Grigoriym/esp32-desk-display/enclosure/renders/enclosure-back.png

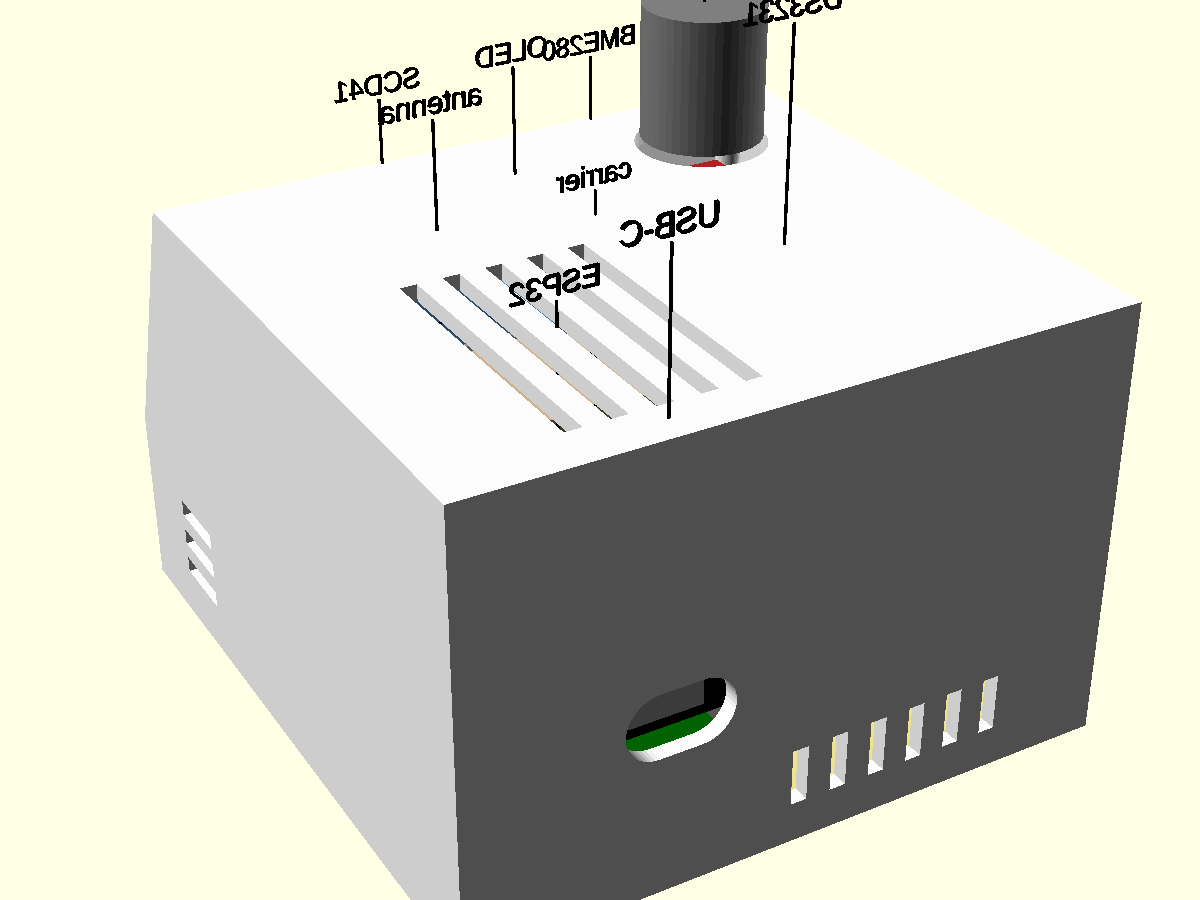
enclosure/renders/enclosure-back.png
