Grigoriym/esp32-desk-display/enclosure/renders/enclosure-section.png

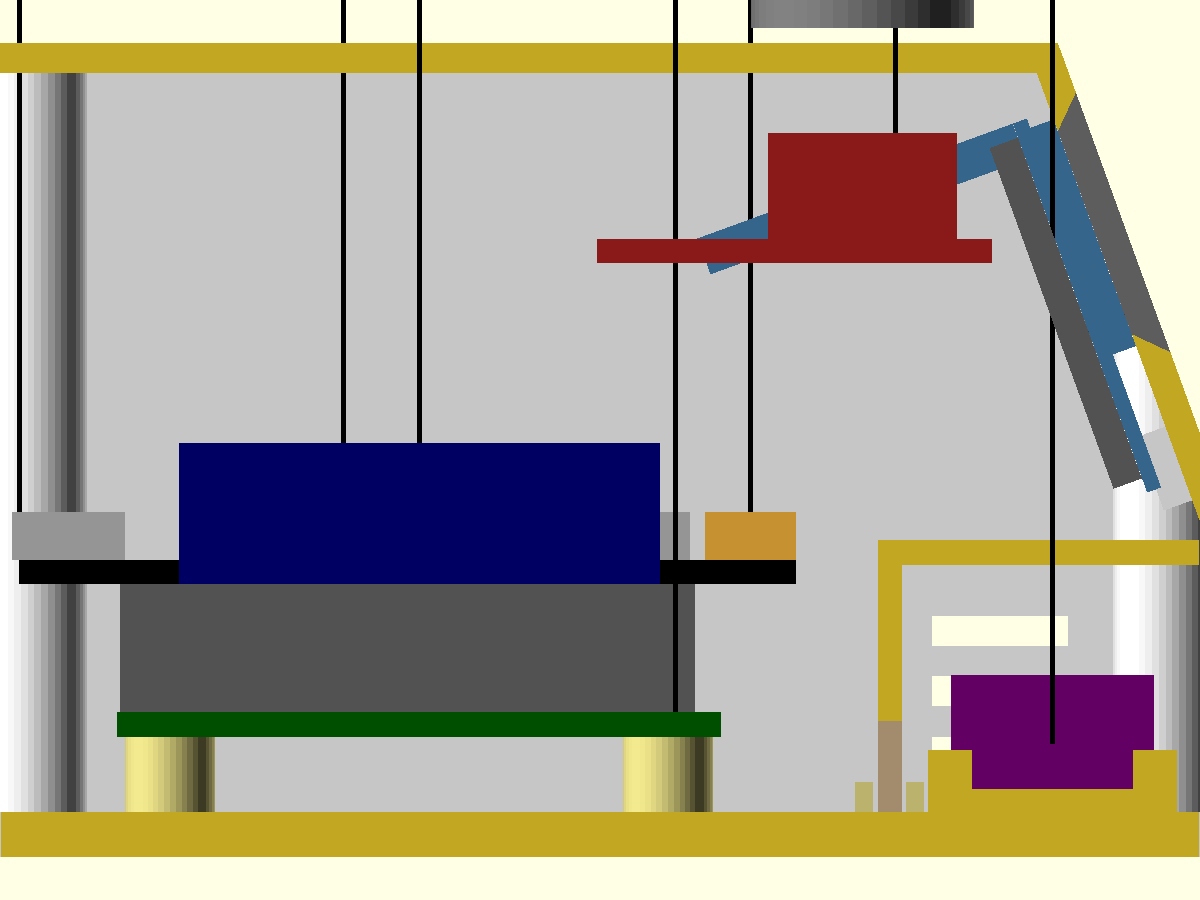
enclosure/renders/enclosure-section.png
