Grigoriym/esp32-desk-display/enclosure/renders/enclosure_v3-top.png

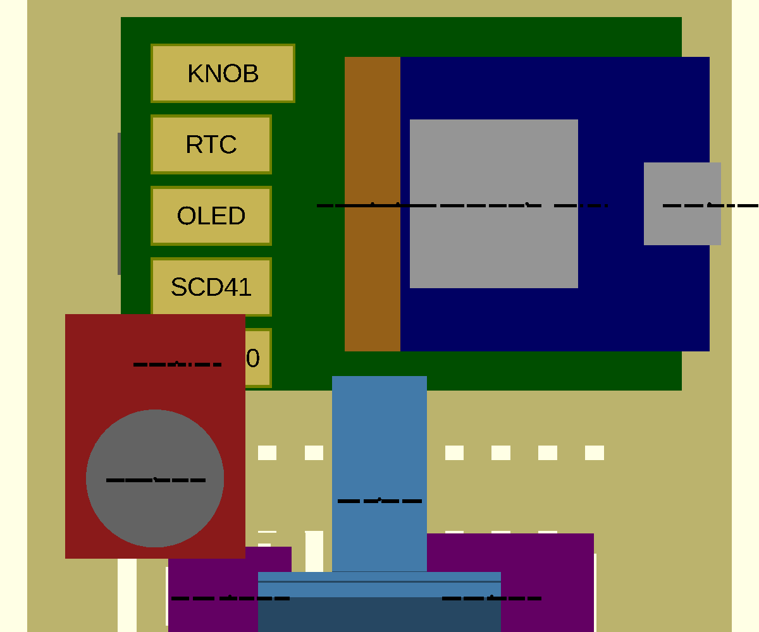
enclosure/renders/enclosure_v3-top.png
