Grigoriym/esp32-desk-display/main/display.h

#pragma once

#include <stdbool.h>
#include "esp_err.h"
#include "driver/i2c_master.h"

// SSD1315/SSD1306 128x64 OLED, page-addressing mode.
// Font covers A-Z, 0-9, ':', '-' and '/'; anything else renders as blank.

// Probes the bus for the display at 0x3C/0x3D, runs the init sequence.
esp_err_t display_init(i2c_master_bus_handle_t bus);

// Blanks the whole panel.
esp_err_t display_clear(void);

// Turns the panel off (sleep, 0xAE) or back on (0xAF). Its RAM keeps what
// was drawn, and drawing while off still updates it for when it comes back.
esp_err_t display_set_on(bool on);

// Draws text centered on the given page (0-7), 8px rows each.
esp_err_t display_draw_text(int page, const char *text);

// Draws left flush against the left edge and right flush against the right
// edge of the given page. Either may be NULL/empty.
esp_err_t display_draw_text_columns(int page, const char *left, const char *right);

// Draws an 8x8 bitmap (column-major, one byte per column) centered on the
// given page. icon may be NULL to blank the page instead.
esp_err_t display_draw_icon(int page, const uint8_t *icon);

// Draws an 8x8 icon immediately followed by text, the pair centered together
// on the given page. Either icon or text may be NULL/empty to draw just the
// other one.
esp_err_t display_draw_icon_and_text(int page, const uint8_t *icon, const char *text);
