Grigoriym/esp32-desk-display/main/wifi.c

#include "wifi.h"
#include "wifi_secrets.h"
#include "esp_wifi.h"
#include "esp_event.h"
#include "esp_log.h"
#include "nvs_flash.h"
#include "freertos/FreeRTOS.h"
#include "freertos/event_groups.h"

static const char *TAG = "wifi";
static EventGroupHandle_t s_wifi_event_group;

#define WIFI_CONNECTED_BIT BIT0

static void event_handler(void *arg, esp_event_base_t event_base, int32_t event_id, void *event_data)
{
    if (event_base == WIFI_EVENT && event_id == WIFI_EVENT_STA_START) {
        esp_wifi_connect();
    } else if (event_base == WIFI_EVENT && event_id == WIFI_EVENT_STA_DISCONNECTED) {
        xEventGroupClearBits(s_wifi_event_group, WIFI_CONNECTED_BIT);
        ESP_LOGW(TAG, "disconnected, retrying...");
        esp_wifi_connect();
    } else if (event_base == IP_EVENT && event_id == IP_EVENT_STA_GOT_IP) {
        ip_event_got_ip_t *event = (ip_event_got_ip_t *)event_data;
        ESP_LOGI(TAG, "got IP: " IPSTR, IP2STR(&event->ip_info.ip));
        xEventGroupSetBits(s_wifi_event_group, WIFI_CONNECTED_BIT);
    }
}

esp_err_t wifi_connect(int timeout_ms)
{
    esp_err_t err = nvs_flash_init();
    if (err == ESP_ERR_NVS_NO_FREE_PAGES || err == ESP_ERR_NVS_NEW_VERSION_FOUND) {
        ESP_ERROR_CHECK(nvs_flash_erase());
        err = nvs_flash_init();
    }
    ESP_ERROR_CHECK(err);

    s_wifi_event_group = xEventGroupCreate();

    ESP_ERROR_CHECK(esp_netif_init());
    ESP_ERROR_CHECK(esp_event_loop_create_default());
    esp_netif_create_default_wifi_sta();

    wifi_init_config_t cfg = WIFI_INIT_CONFIG_DEFAULT();
    ESP_ERROR_CHECK(esp_wifi_init(&cfg));

    ESP_ERROR_CHECK(esp_event_handler_register(WIFI_EVENT, ESP_EVENT_ANY_ID, &event_handler, NULL));
    ESP_ERROR_CHECK(esp_event_handler_register(IP_EVENT, IP_EVENT_STA_GOT_IP, &event_handler, NULL));

    wifi_config_t wifi_config = {
        .sta =
            {
                .ssid = WIFI_SSID,
                .password = WIFI_PASSWORD,
            },
    };
    ESP_ERROR_CHECK(esp_wifi_set_mode(WIFI_MODE_STA));
    ESP_ERROR_CHECK(esp_wifi_set_config(WIFI_IF_STA, &wifi_config));
    ESP_ERROR_CHECK(esp_wifi_start());

    ESP_LOGI(TAG, "connecting to %s...", WIFI_SSID);
    EventBits_t bits = xEventGroupWaitBits(s_wifi_event_group, WIFI_CONNECTED_BIT, pdFALSE, pdTRUE,
                                           pdMS_TO_TICKS(timeout_ms));
    if (!(bits & WIFI_CONNECTED_BIT)) {
        ESP_LOGW(TAG, "not connected after %d ms, still retrying in the background", timeout_ms);
        return ESP_ERR_TIMEOUT;
    }
    return ESP_OK;
}

bool wifi_is_connected(void)
{
    return s_wifi_event_group && (xEventGroupGetBits(s_wifi_event_group) & WIFI_CONNECTED_BIT);
}

bool wifi_rssi(int *out)
{
    wifi_ap_record_t ap;
    if (!wifi_is_connected() || esp_wifi_sta_get_ap_info(&ap) != ESP_OK) return false;
    *out = (int)ap.rssi; // dBm, genuinely signed
    return true;
}
