Grigoriym/esp32-desk-display/main/bme280.h

#pragma once

#include "esp_err.h"
#include "bme280_reading.h"
#include "driver/i2c_master.h"

// Looks for a BME280 at 0x76/0x77, checks its chip ID (rejects a BMP280,
// which has no humidity) and loads its factory calibration.
esp_err_t bme280_init(i2c_master_bus_handle_t bus);

// Triggers one forced-mode measurement and waits for it (~10ms).
esp_err_t bme280_read(bme280_reading_t *out);
